maltman23/TV-B-Gone-kit_V2/graphics/TV-B-Gone-kit_V2_prototype.jpg

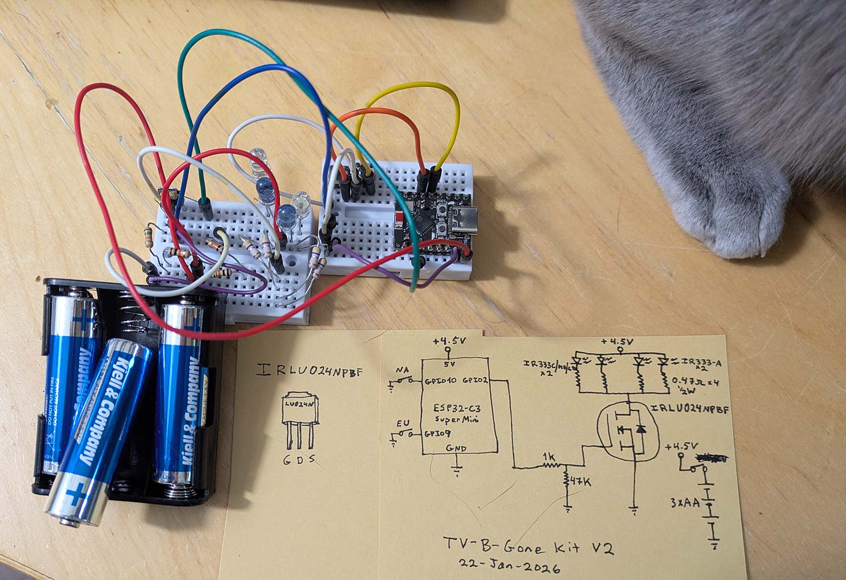
graphics/TV-B-Gone-kit_V2_prototype.jpg
