maltman23/TV-B-Gone-kit_V2/graphics/TV-B-Gone_turning_TVs_off_graphic.png

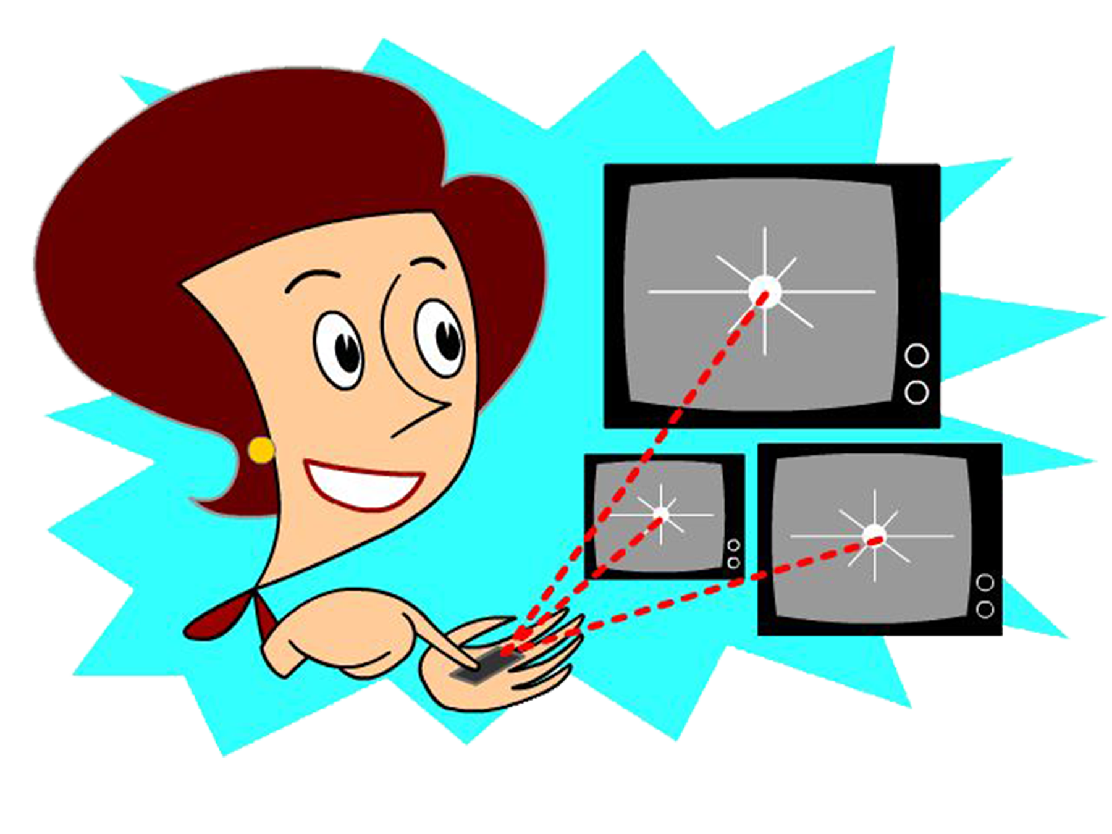
graphics/TV-B-Gone_turning_TVs_off_graphic.png
