maltman23/TV-B-Gone-kit_V2/firmware/TV-B-Gone_kit_V2/WORLDcodes.cpp

/**************************************************

TV-B-Gone WORLDcodes for Arduino version 0.002

  The original TV-B-Gone kit firmware is:
  TV-B-Gone Firmware version 1.2
       for use with ATtiny85v and TV-B-Gone kit v1.2 hardware
       (c) Mitch Altman + Limor Fried 2009

  3-December-2009
  Ported to Arduino by Ken Shirriff
  http://arcfn.com

  2-September-2015
  Mitch Altman
  Updated definitions for
       struct IrCode *EUpowerCodes[] = {
  and
       struct IrCode *NApowerCodes[] = {
  so that the sketch will compile with Arduino 1.6.5 software.
  The new definitions are:
       extern "C" struct IrCode * const EUpowerCodes[] = {
  and
       extern "C" struct IrCode * const EUpowerCodes[] = {

  20-Jun-2025
  BenBE and Mitch Altman
  The POWER-Codes here are the same as the original compressed codes
       except the indices to the On-Time/Off-Time pairs table for each Off-Code are no longer data-compressed.
  The "convertWorldCodes.py" script converts from the original to the new version of the Off-Codes in the "extractedWorldCodeData.json" file

  25-Jun-2025
  This "json2cppConvert.py" script to create the new "WORLDcodes.txt" file from the "extractedWorldCodesData.json" file
       was written by Mitch Altman

  17-Jul-2025
  Mitch Altman
  I'm having trouble getting the ESP32-C3 compiler for Arduino to accept variable pointers to constants 
     (even through the same code compiles fine, and works fine, when compiled for Arduino Uno boards),
  The code compiles and works fine if the entire database here in WORLDcodes.cpp is variables (and not constants).
  Updated comments.

  21-Jan-2026   Mitch Altman
  Updated for ESP32-C3 Super Mini board



  Creative Commons CC BY-SA 4.0
  This license enables reusers to distribute, remix, adapt, and build
  upon the material in any medium or format, so long as attribution is
  given to the creator. The license allows for commercial use. If you remix, adapt, or
  build upon the material, you must license the modified material under identical
  terms. CC BY-SA includes the following elements:
     BY: credit must be given to the creator.
     SA: Adaptations must be shared under the same terms.

**************************************************/



#include <cstdint>      // needed for ESP32 on the Arduino IDE (must be declared before any other #include)
#include "main.h"

/**************************************************

   Table of POWER codes
   Codes captured from Generation 3 TV-B-Gone by Limor Fried & Mitch Altman

   This version of WORLDcodes does not compress the indices to the On-Time/Off-Time pair tables for each POWER-Code.

   Each POWER-Code consists of three tables:
      * 'Pairs' table -- a table of unique On-Time/Off-Time pairs for the POWER-Code -- e.g.: code_na000Pairs[]
      * 'Sequence' table -- table of indices to the On-Time/Off-Time Pairs table     -- e.g.: code_na000Sequence[]
      * 'Code'  table                                                                -- e.g.: code_na000Code[]
           that gives:
              ** the POWER-Code's Carrier Frequency
              ** number of On-Time/Off-Time pairs in the transmission sequence that comprise the POWER-Code
              ** address of the Pairs table (which contains the POWER-Code's unique On-Time/Off-Time pairs)
              ** address of the sequence table (which contains the sequence of indices to the On-Time/Off-Time pairs in the pairs table)
   To transmit a code:
      - Grab the info for this POWER-Code from the 'Code' table
      - Set up hardware timers on the microcontroller for this POWER-Code's Carrier Frequency
      - Go through the 'Sequence' table, one index at a time,
           to transmit each On-Time/Off-Time pair in the 'Pairs' table in the appropriate order


   Example POWER-Code transmission (using code_na000):
      - From the 'Code' table we can see that the Carrier Frequency is 38,400Hz and that there are 26 On-Time/Off-Time pairs.
      - After setting up the microcontroller's timers for the Carrier Frequency, we can start transmitting the POWER-Code.
      - Every POWER-Code is merely a sequence of On-Time/Off-Time pairs.
      - Let's just look at the first three indices from the 'Codes' table
         -- The first index is: 3
               This points to the 4th entry in the 'Pairs' table: 2400, 600
               This means: pulse IR at the Carrier Frequency of 38,400Hz for 2400uS, and then IR off for 600uS.
         -- The second index is: 2
               This points to the 3rd entry in the 'Pairs' table: 1200, 600
               This means: pulse IR at the Carrier Frequency of 38,400Hz for 1200uS, and then IR off for 600uS.
         -- The third index is: 0
               This points to the 1st entry in the 'Pairs' table: 600, 600
               This means: pulse IR at the Carrier Frequency of 38,400Hz for 600uS, and then IR off for 600uS.
      - After going through all 26 On-Time/Off-Time pairs, any TV near you with this POWER-Code will be (pleasantly) OFF.

**************************************************/

// code_na000
//
// table of On-Time/Off-Time pairs
uint32_t code_na000Pairs[] = {
  600, 600,
  600, 27000,
  1200, 600,
  2400, 600,
};
// table of indices to On-Time/Off-Time pairs
uint8_t code_na000Sequence[] = {
  3, 2, 0, 2, 0, 2, 0, 0, 2, 0, 0, 0, 1, 3, 2, 0, 2, 0, 2, 0, 0, 2, 0, 0, 0, 1
};
// POWER-Code table
struct IrCode code_na000Code  = {
  38400,     // carrier frequency
  26,        // number of On-Time/Off-Time pairs in this Off-Code
  code_na000Pairs,
  code_na000Sequence
};


// code_na001
//
// table of On-Time/Off-Time pairs
uint32_t code_na001Pairs[] = {
  500, 1000,
  500, 2000,
  500, 8000,
  4000, 4000,
};
// table of indices to On-Time/Off-Time pairs
uint8_t code_na001Sequence[] = {
  3, 1, 1, 1, 1, 0, 0, 1, 0, 1, 0, 1, 0, 0, 0, 0, 0, 1, 1, 0, 1, 0, 1, 0, 1, 2, 3, 1, 1, 1, 1, 0, 0, 1, 0, 1, 0, 1, 0, 0, 0, 0, 0, 1, 1, 0, 1, 0, 1, 0, 1, 1
};
// POWER-Code table
struct IrCode code_na001Code  = {
  57143,     // carrier frequency
  52,        // number of On-Time/Off-Time pairs in this Off-Code
  code_na001Pairs,
  code_na001Sequence
};


// code_na002
//
// table of On-Time/Off-Time pairs
uint32_t code_na002Pairs[] = {
  420, 460,
  420, 1330,
  420, 75190,
  3470, 1760,
  3470, 1770,
};
// table of indices to On-Time/Off-Time pairs
uint8_t code_na002Sequence[] = {
  3, 0, 1, 0, 0, 0, 0, 0, 0, 0, 0, 0, 0, 0, 1, 0, 0, 0, 0, 0, 0, 0, 0, 0, 1, 0, 0, 0, 0, 0, 0, 0, 0, 1, 0, 1, 1, 1, 1, 0, 0, 1, 0, 1, 1, 1, 1, 0, 1, 2, 4, 0, 1, 0, 0, 0, 0, 0, 0, 0, 0, 0, 0, 0, 1, 0, 0, 0, 0, 0, 0, 0, 0, 0, 1, 0, 0, 0, 0, 0, 0, 0, 0, 1, 0, 1, 1, 1, 1, 0, 0, 1, 0, 1, 1, 1, 1, 0, 1, 0
};
// POWER-Code table
struct IrCode code_na002Code  = {
  37037,     // carrier frequency
  100,       // number of On-Time/Off-Time pairs in this Off-Code
  code_na002Pairs,
  code_na002Sequence
};


// code_na003
//
// table of On-Time/Off-Time pairs
uint32_t code_na003Pairs[] = {
  260, 1850,
  270, 800,
  270, 1850,
  270, 45490,
};
// table of indices to On-Time/Off-Time pairs
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
uint8_t code_eu067Sequence[] = {
  1, 0, 0, 1, 0, 2, 1, 0, 0, 1, 0, 2
};
// POWER-Code table
struct IrCode code_eu067Code  = {
  38462,     // carrier frequency
  12,        // number of On-Time/Off-Time pairs in this Off-Code
  code_eu067Pairs,
  code_eu067Sequence
};


// code_eu068
//
// table of On-Time/Off-Time pairs
uint32_t code_eu068Pairs[] = {
  490, 2630,
  500, 540,
  500, 1080,
  500, 2630,
  500, 20290,
  500, 101990,
  1000, 1100,
};
// table of indices to On-Time/Off-Time pairs
uint8_t code_eu068Sequence[] = {
  0, 1, 1, 1, 1, 1, 1, 1, 1, 1, 4, 3, 2, 1, 1, 1, 1, 6, 1, 1, 5, 3, 2, 1, 1, 1, 1, 6, 1, 1, 1
};
// POWER-Code table
struct IrCode code_eu068Code  = {
  38610,     // carrier frequency
  31,        // number of On-Time/Off-Time pairs in this Off-Code
  code_eu068Pairs,
  code_eu068Sequence
};


// code_eu069
//
// table of On-Time/Off-Time pairs
uint32_t code_eu069Pairs[] = {
  40, 4990,
  40, 7500,
  40, 49990,
};
// table of indices to On-Time/Off-Time pairs
uint8_t code_eu069Sequence[] = {
  0, 0, 1, 1, 1, 1, 1, 0, 0, 0, 1, 2, 0, 0, 1, 1, 1, 1, 1, 0, 0, 0, 1
};
// POWER-Code table
struct IrCode code_eu069Code  = {
  0,         // carrier frequency
  23,        // number of On-Time/Off-Time pairs in this Off-Code
  code_eu069Pairs,
  code_eu069Sequence
};


// code_eu070
//
// table of On-Time/Off-Time pairs
uint32_t code_eu070Pairs[] = {
  40, 4990,
  40, 7500,
  40, 49990,
};
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
